NordThing/ATLASfreelss/STL files/camera_bracket.stl

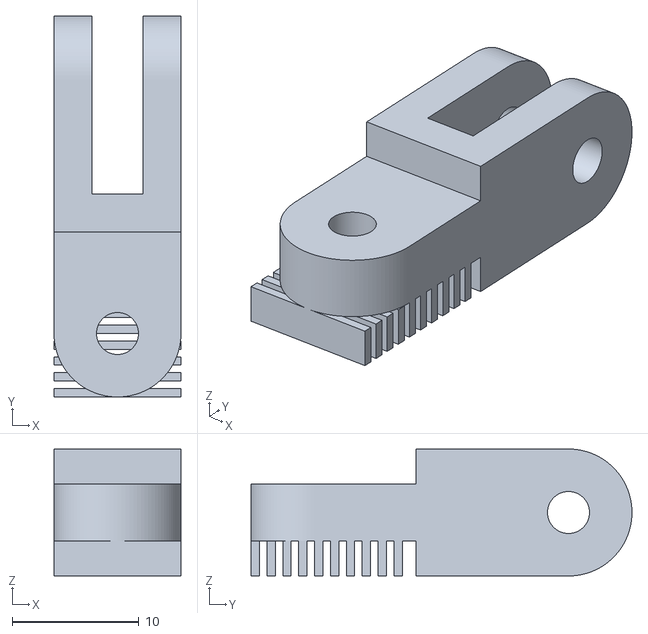
[picture p17: CAD file, 2022-07-26]
STL files/camera_bracket.stl
10.0 x 30.0 x 10.0
