NordThing/ATLASfreelss/STL files/camera_tower.stl

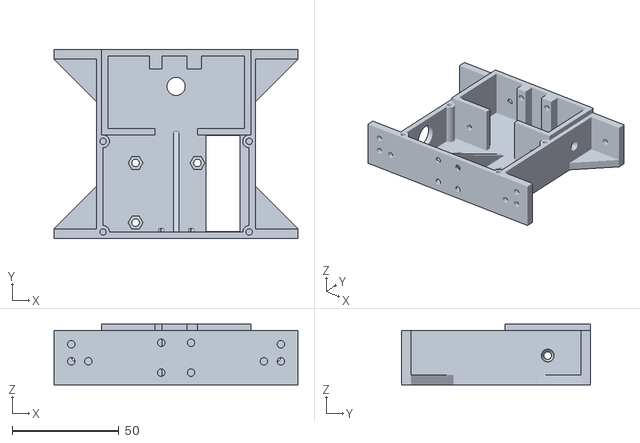
[picture p18: CAD file, 2022-07-26]
STL files/camera_tower.stl
114.4 x 88.5 x 28.4
