NordThing/ATLASfreelss/STL files/cross_bar.stl

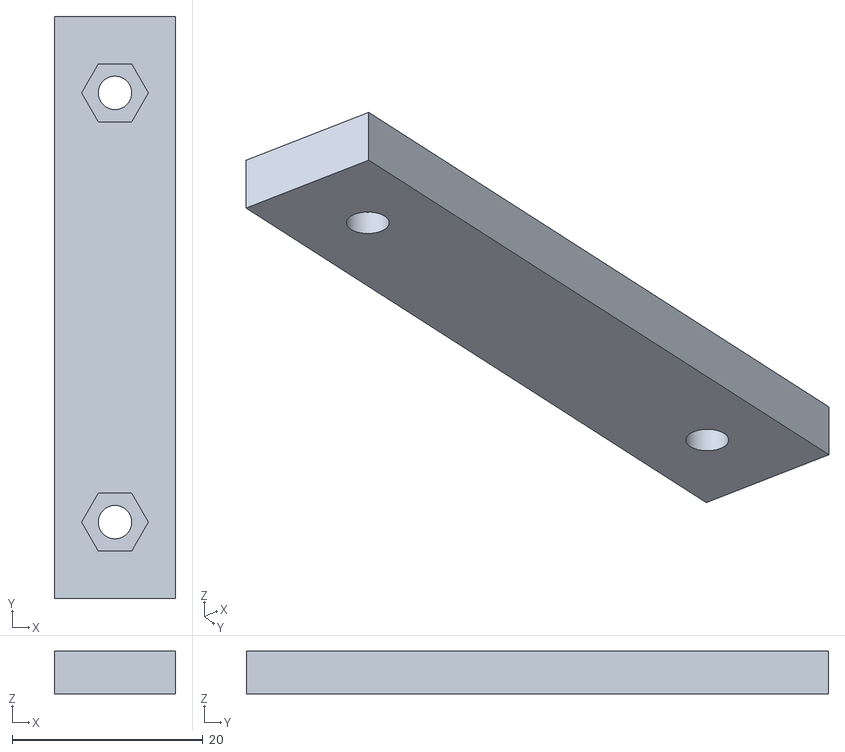
[picture p19: CAD file, 2022-07-26]
STL files/cross_bar.stl
12.7 x 61.0 x 4.50
