NordThing/ATLASfreelss/STL files/rpi_case_bplus_lower.stl

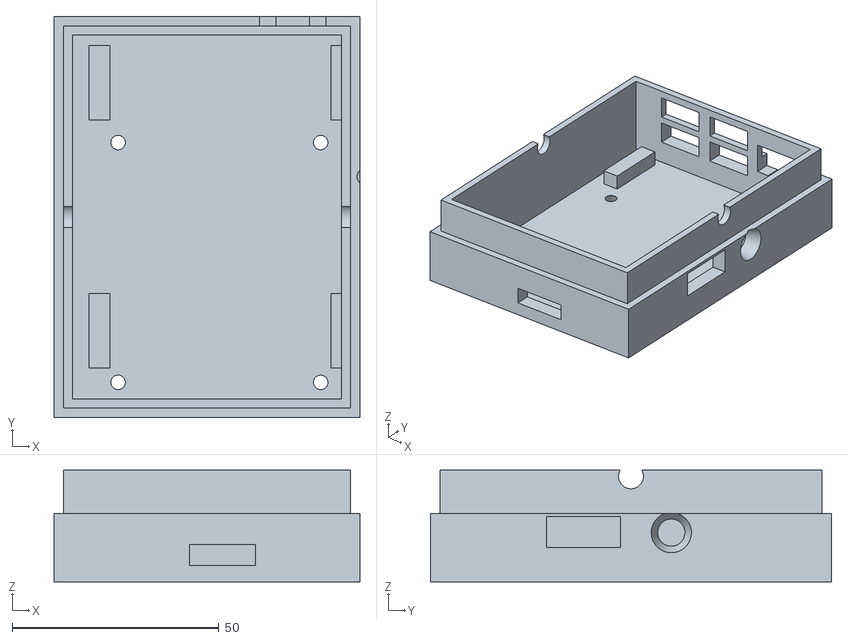
[picture p20: CAD file, 2022-07-26]
STL files/rpi_case_bplus_lower.stl
74.0 x 97.0 x 27.0
