NordThing/ATLASfreelss/STL files/frame_section_2.stl

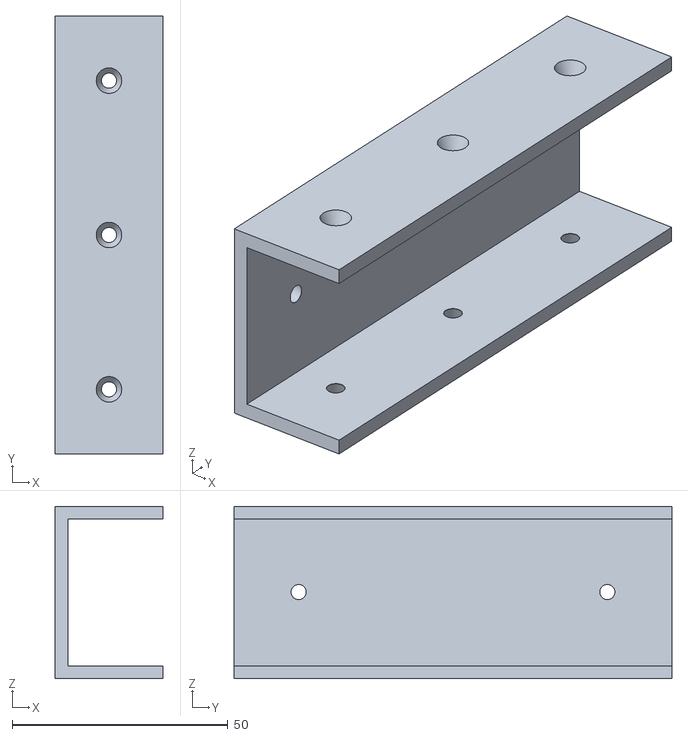
[picture p21: CAD file, 2022-07-26]
STL files/frame_section_2.stl
25.0 x 101.6 x 40.0
