NordThing/ATLASfreelss/STL files/camera_case_back.stl

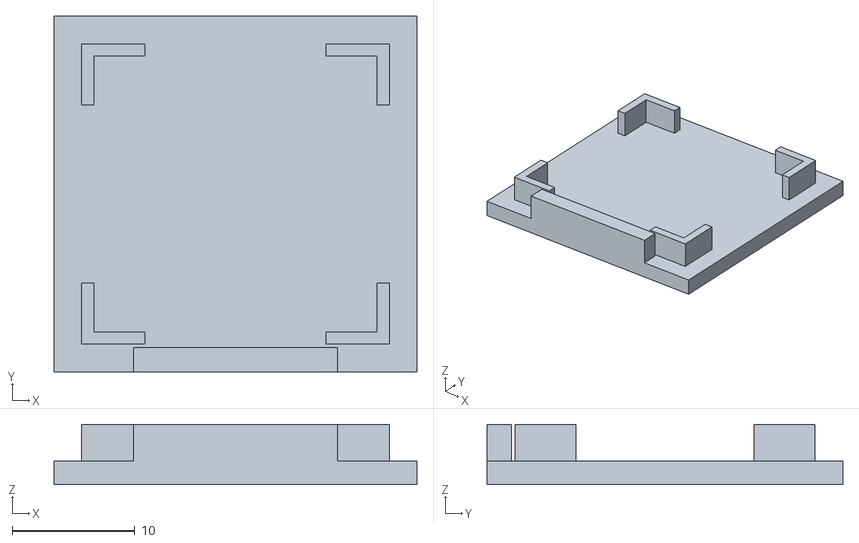
[picture p22: CAD file, 2022-07-26]
STL files/camera_case_back.stl
29.6 x 29.0 x 4.90
