NordThing/ATLASfreelss/STL files/camera_arm.stl

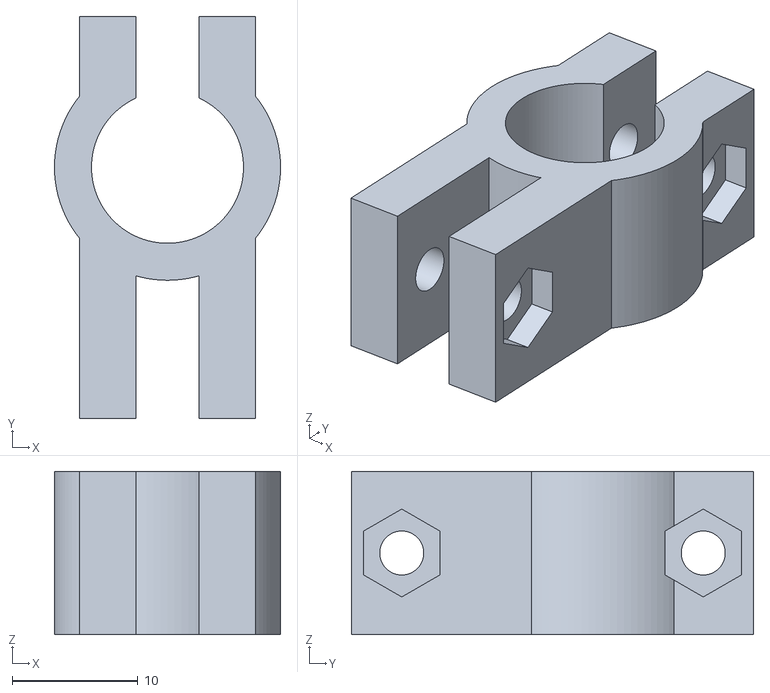
[picture p23: CAD file, 2022-07-26]
STL files/camera_arm.stl
18.0 x 32.0 x 13.0
