NordThing/ATLASfreelss/STL files/turn_table_d7p5.stl

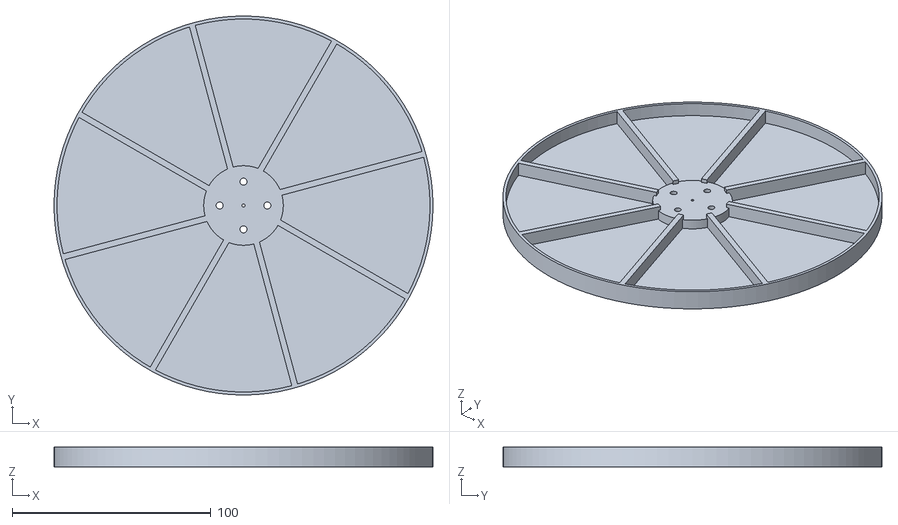
[picture p24: CAD file, 2022-07-26]
STL files/turn_table_d7p5.stl
190.5 x 190.5 x 10.0
