NordThing/ATLASfreelss/STL files/left_laser_hinge_holder.stl

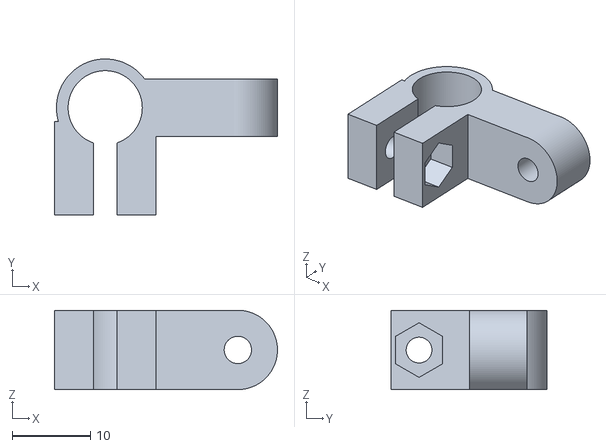
[picture p25: CAD file, 2022-07-26]
STL files/left_laser_hinge_holder.stl
28.6 x 20.0 x 10.2
