NordThing/ATLASfreelss/STL files/rpi_case_bplus_upper.stl

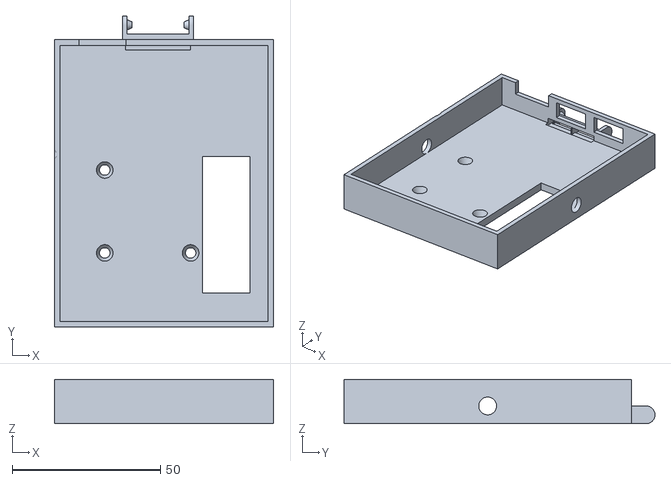
[picture p26: CAD file, 2022-07-26]
STL files/rpi_case_bplus_upper.stl
74.0 x 105.0 x 15.0
