NordThing/ATLASfreelss/STL files/rpi_case_b_lower.stl

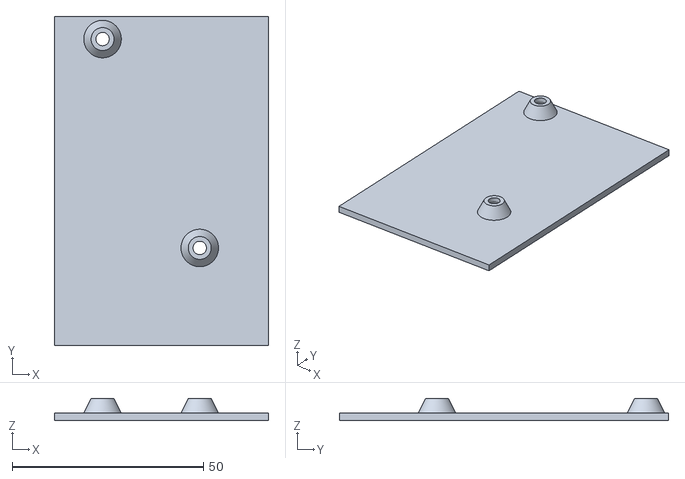
[picture p27: CAD file, 2022-07-26]
STL files/rpi_case_b_lower.stl
56.0 x 86.0 x 5.80
