NordThing/ATLASfreelss/STL files/camera_case_front.stl

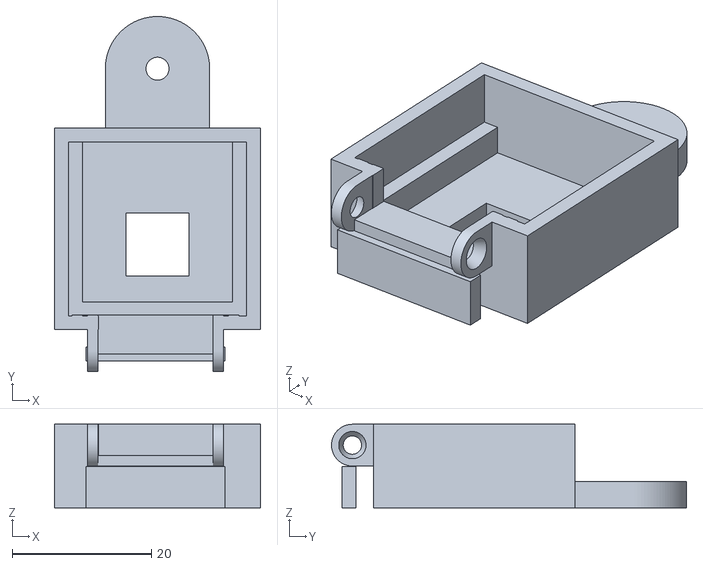
[picture p28: CAD file, 2022-07-26]
STL files/camera_case_front.stl
29.6 x 51.0 x 12.0
