NordThing/ATLASfreelss/STL files/frame_connector.stl

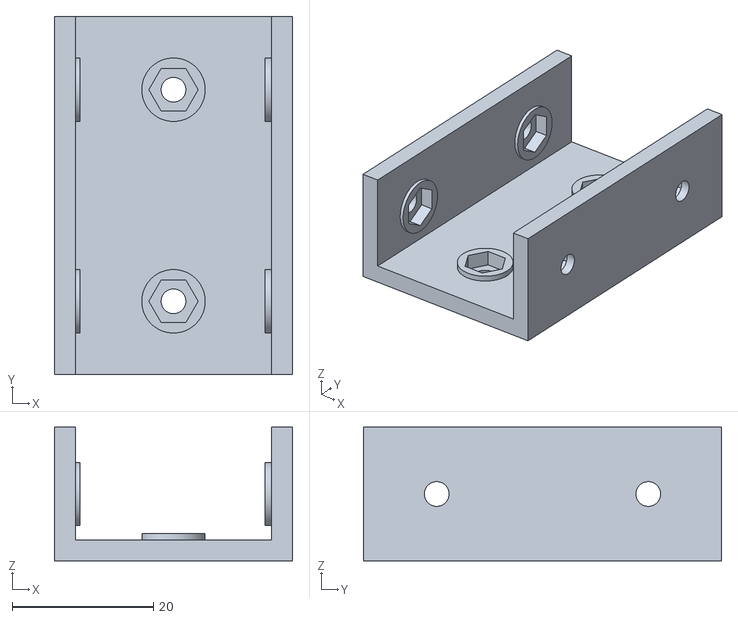
[picture p29: CAD file, 2022-07-26]
STL files/frame_connector.stl
33.8 x 50.8 x 19.0
