NordThing/ATLASfreelss/STL files/calibration_item.stl

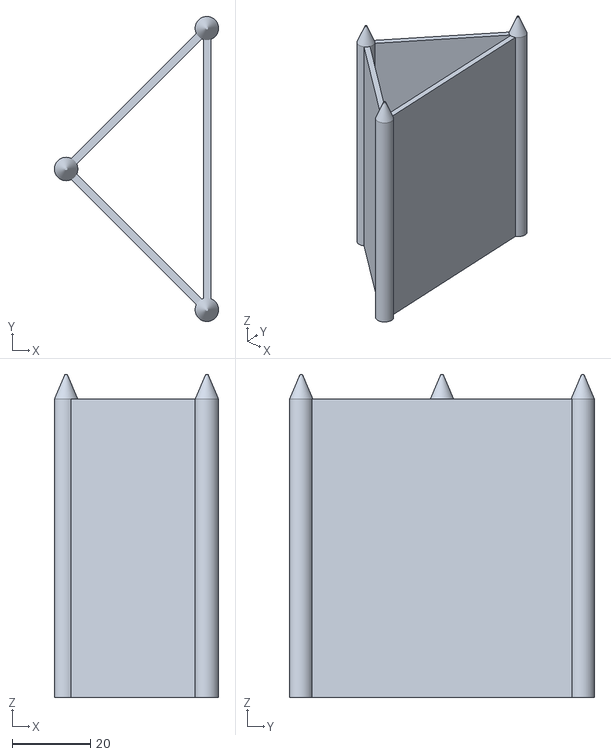
[picture p30: CAD file, 2022-07-26]
STL files/calibration_item.stl
41.9 x 77.8 x 82.5
