NordThing/ATLASfreelss/STL files/table_coupler.stl

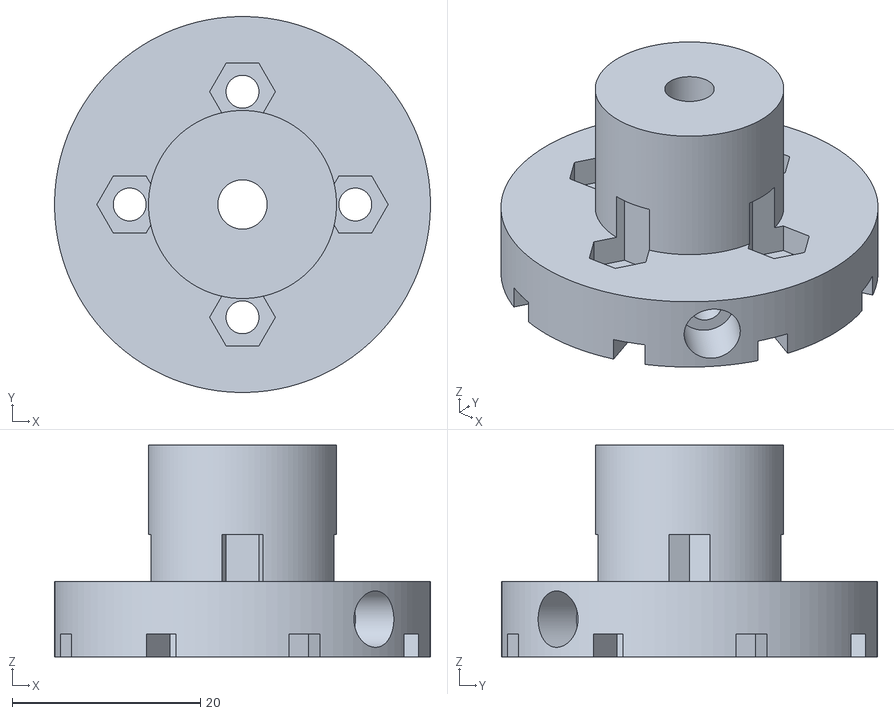
[picture p31: CAD file, 2022-07-26]
STL files/table_coupler.stl
40.0 x 40.0 x 22.5
