NordThing/ATLASfreelss/STL files/camera_shaft.stl

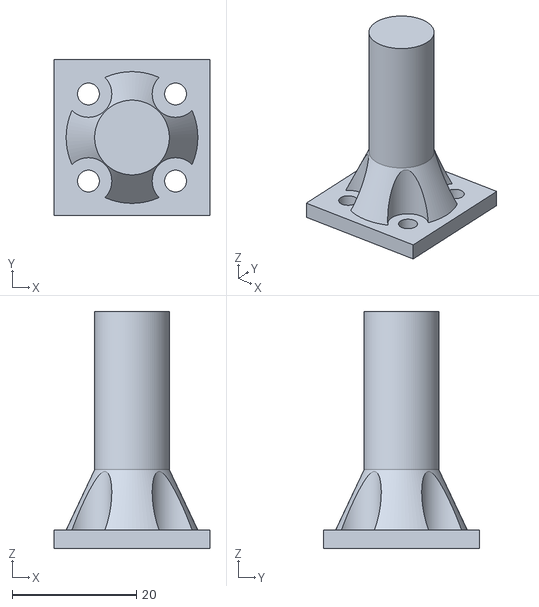
[picture p32: CAD file, 2022-07-26]
STL files/camera_shaft.stl
25.0 x 25.0 x 38.1
